DanNixon/GoogleMusicRadio/KiCAD/MainBoard/MainBoard.sch

## KiCad design KiCAD/MainBoard/MainBoard.sch (2013-06-19)

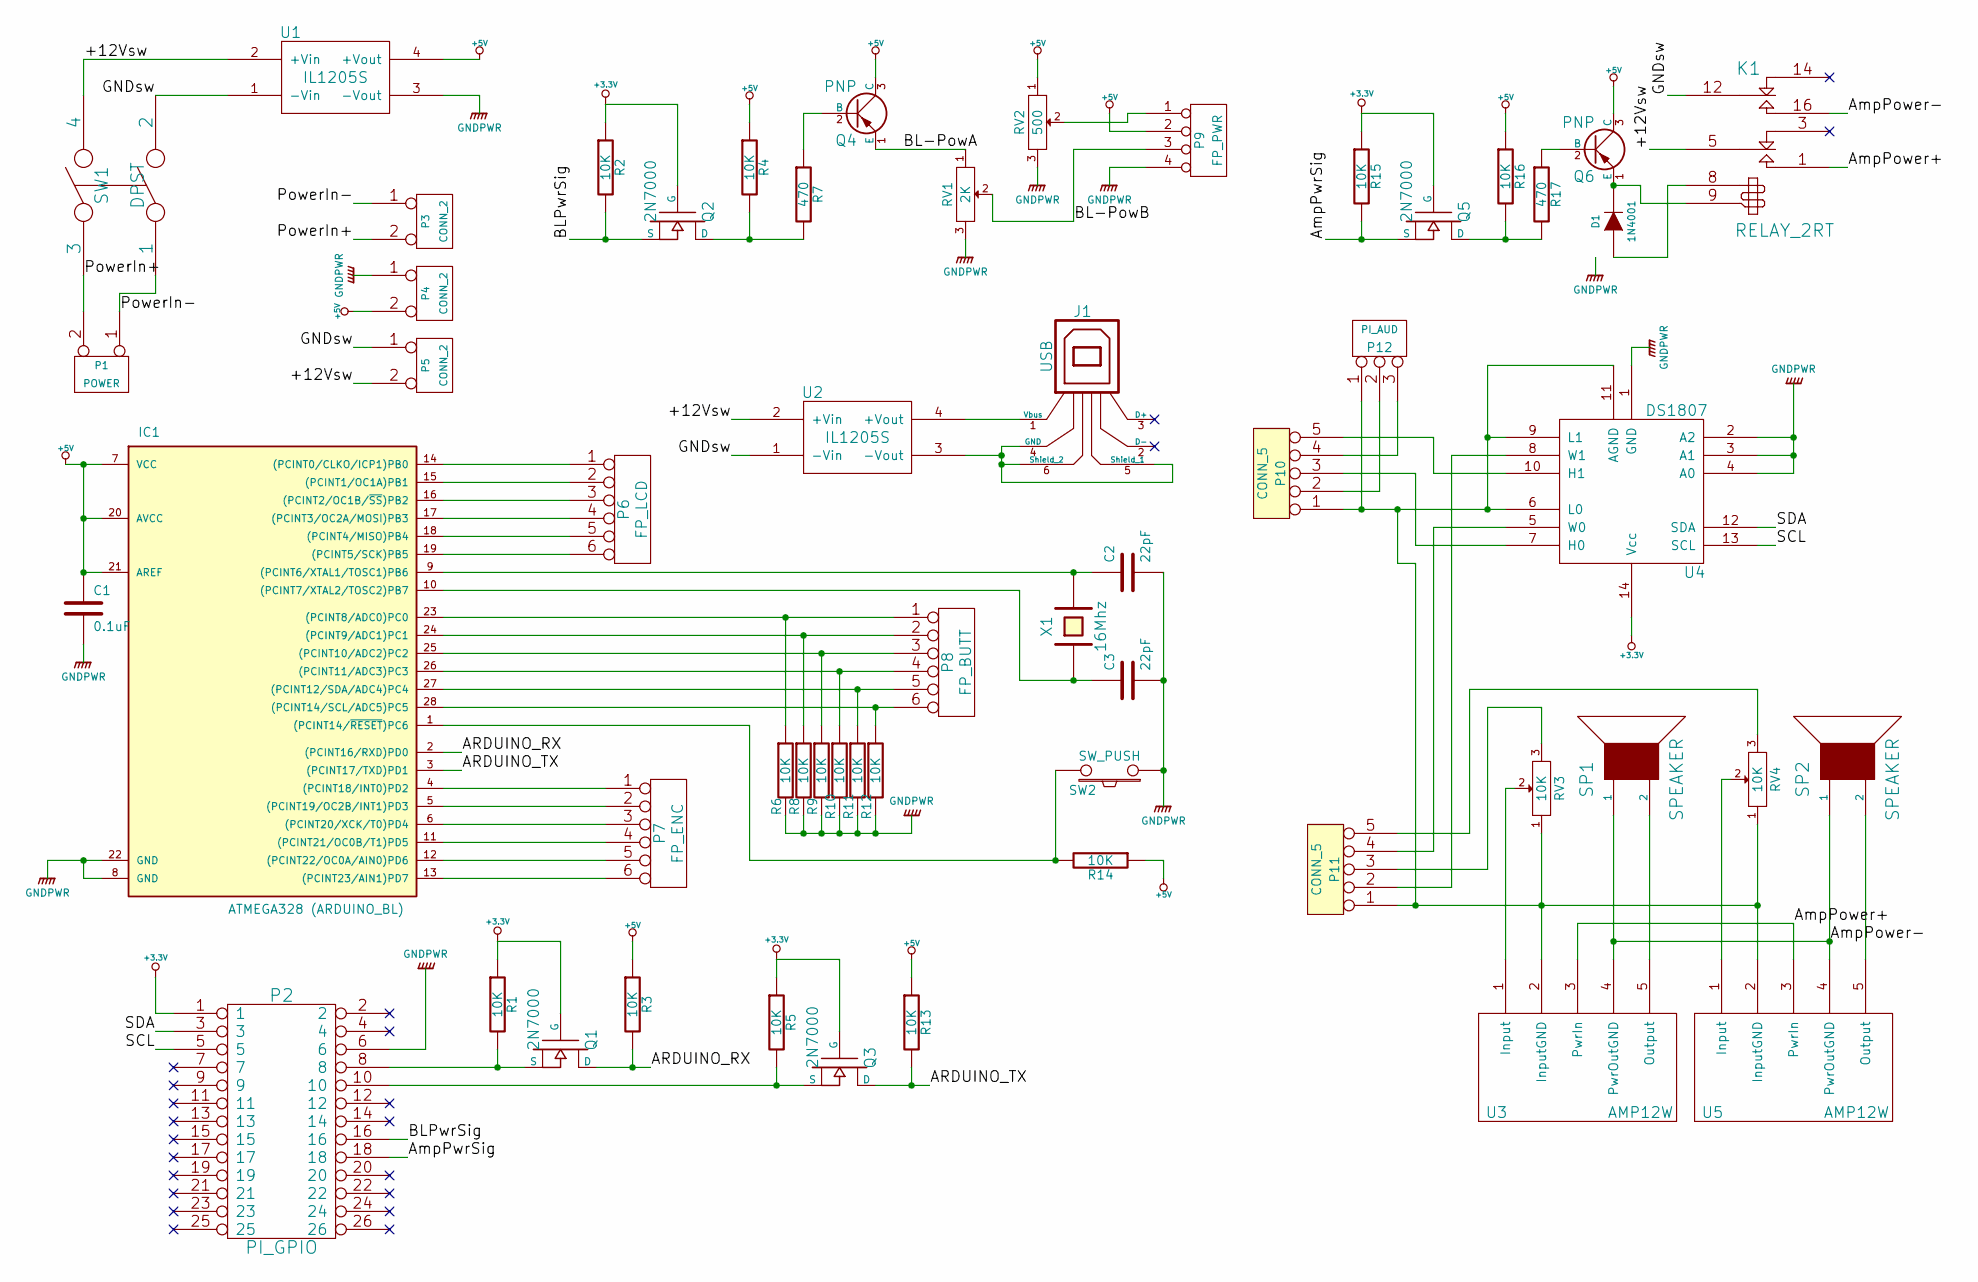
[picture p12: schematic MainBoard.sch]

Parts:
C1: 0.1uF
C2, C3: 22pF
D1: 1N4001
IC1: ATMEGA328 (ARDUINO_BL); DIL28
J1: USB
K1: RELAY_2RT
P1: POWER
P2: PI_GPIO
P3, P4, P5: CONN_2
P6: FP_LCD
P7: FP_ENC
P8: FP_BUTT
P9: FP_PWR
P10, P11: CONN_5
P12: PI_AUD
Q1, Q2, Q3, Q5: 2N7000
Q4, Q6: PNP
R1, R2, R3, R4, R5, R6, R8, R9, R10, R11, R12, R13, R14, R15, R16: 10K
R7, R17: 470
RV1: 2K
RV2: 500
RV3, RV4: 10K
SP1, SP2: SPEAKER
SW1: DPST
SW2: SW_PUSH
U1, U2: IL1205S
U3, U5: AMP12W
U4: DS1807
X1: 16Mhz

Connections:
+3.3V: P2.1, Q1.G, Q2.G, Q3.G, Q5.G, R1.1, R2.1, R5.1, R15.1, U4.14 (Vcc)
+5V: C1.1, IC1.7 (VCC), IC1.20 (AVCC), IC1.21 (AREF), P4.2 (PM), P9.2, Q4.3 (C), Q6.3 (C), R3.1, R4.1, R13.1, R14.1, R16.1, RV2.1, U1.4 (+Vout)
+12Vsw: K1.5 (C1), P5.2 (PM), SW1.4, U1.2 (+Vin), U2.2 (+Vin)
ARDUINO_RX: IC1.2 ((PCINT16/RXD)PD0), Q1.D, R3.2
ARDUINO_TX: IC1.3 ((PCINT17/TXD)PD1), Q3.D, R13.2
AmpPower+: K1.1 (T1), U3.3 (PwrIn), U5.3 (PwrIn)
AmpPower-: K1.16 (T2), SP1.1, SP2.1, U3.4 (PwrOutGND), U5.4 (PwrOutGND)
AmpPwrSig: P2.18, Q5.S, R15.2
BL-PowA: Q4.1 (E), RV1.1
BL-PowB: P9.3, RV1.2
BLPwrSig: P2.16, Q2.S, R2.2
GNDPWR: C1.2, C2.2, C3.2, IC1.8 (GND), IC1.22 (GND), P2.6, P4.1, P9.4, R6.2, R8.2, R9.2, R10.2, R11.2, R12.2, RV1.3, RV2.3, SW2.1, U1.3 (-Vout), U4.1 (GND), U4.2 (A2), U4.3 (A1), U4.4 (A0)
GNDsw: K1.12 (C2), P5.1, SW1.2, U1.1 (-Vin), U2.1 (-Vin)
unnamed: C2.1, IC1.9 ((PCINT6/XTAL1/TOSC1)PB6), X1.2
unnamed: C3.1, IC1.10 ((PCINT7/XTAL2/TOSC2)PB7), X1.1
unnamed: D1.1 (A), K1.8
unnamed: D1.2 (K), K1.9, Q6.1 (E)
unnamed: IC1.1 ((PCINT14/~RESET~)PC6), R14.2, SW2.2
unnamed: IC1.4 ((PCINT18/INT0)PD2), P7.1
unnamed: IC1.5 ((PCINT19/OC2B/INT1)PD3), P7.2
unnamed: IC1.6 ((PCINT20/XCK/T0)PD4), P7.3
unnamed: IC1.11 ((PCINT21/OC0B/T1)PD5), P7.4
unnamed: IC1.12 ((PCINT22/OC0A/AIN0)PD6), P7.5
unnamed: IC1.13 ((PCINT23/AIN1)PD7), P7.6
unnamed: IC1.14 ((PCINT0/CLKO/ICP1)PB0), P6.1
unnamed: IC1.15 ((PCINT1/OC1A)PB1), P6.2
unnamed: IC1.16 ((PCINT2/OC1B/~SS~)PB2), P6.3
unnamed: IC1.17 ((PCINT3/OC2A/MOSI)PB3), P6.4
unnamed: IC1.18 ((PCINT4/MISO)PB4), P6.5
unnamed: IC1.19 ((PCINT5/SCK)PB5), P6.6
unnamed: IC1.23 ((PCINT8/ADC0)PC0), P8.1, R6.1
unnamed: IC1.24 ((PCINT9/ADC1)PC1), P8.2, R8.1
unnamed: IC1.25 ((PCINT10/ADC2)PC2), P8.3, R9.1
unnamed: IC1.26 ((PCINT11/ADC3)PC3), P8.4, R10.1
unnamed: IC1.27 ((PCINT12/SDA/ADC4)PC4), P8.5, R11.1
unnamed: IC1.28 ((PCINT14/SCL/ADC5)PC5), P8.6, R12.1
unnamed: J1.1 (Vbus), U2.4 (+Vout)
unnamed: J1.4 (GND), J1.5 (Shield_1), J1.6 (Shield_2), U2.3 (-Vout)
unnamed: P2.8, Q1.S, R1.2
unnamed: P2.10, Q3.S, R5.2
unnamed: P9.1, RV2.2
unnamed: P10.1, P11.1, P12.1, RV3.1, RV4.1, U3.2 (InputGND), U4.6 (L0), U4.9 (L1), U4.11 (AGND), U5.2 (InputGND)
unnamed: P10.2, P12.2 (PM)
unnamed: P10.3, U4.7 (H0)
unnamed: P10.4, P12.3
unnamed: P10.5, U4.10 (H1)
unnamed: P11.2, U4.8 (W1)
unnamed: P11.3, RV3.3
unnamed: P11.4, U4.5 (W0)
unnamed: P11.5, RV4.3
unnamed: Q2.D, R4.2, R7.2
unnamed: Q4.2 (B), R7.1
unnamed: Q5.D, R16.2, R17.2
unnamed: Q6.2 (B), R17.1
unnamed: RV3.2, U3.1 (Input)
unnamed: RV4.2, U5.1 (Input)
unnamed: SP1.2, U3.5 (Output)
unnamed: SP2.2, U5.5 (Output)
PowerIn+: P1.2 (PM), P3.2 (PM), SW1.3
PowerIn-: P1.1, P3.1, SW1.1
SCL: P2.5, U4.13 (SCL)
SDA: P2.3, U4.12 (SDA)
